antinucleus/pen-plotter/Electrical Design/Media/EasyEDA Design/Bottom.png

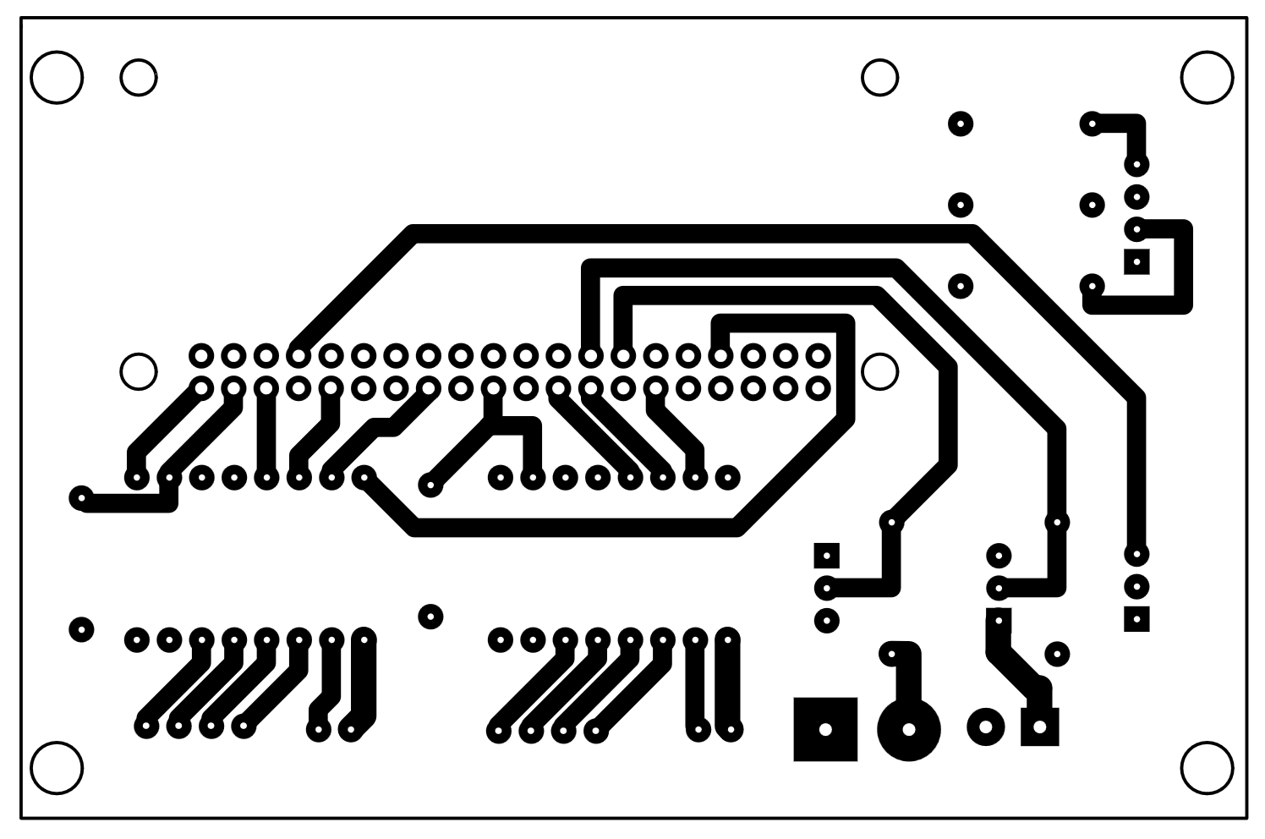
Electrical Design/Media/EasyEDA Design/Bottom.png
