antinucleus/pen-plotter/Electrical Design/Media/EasyEDA Design/Top.png

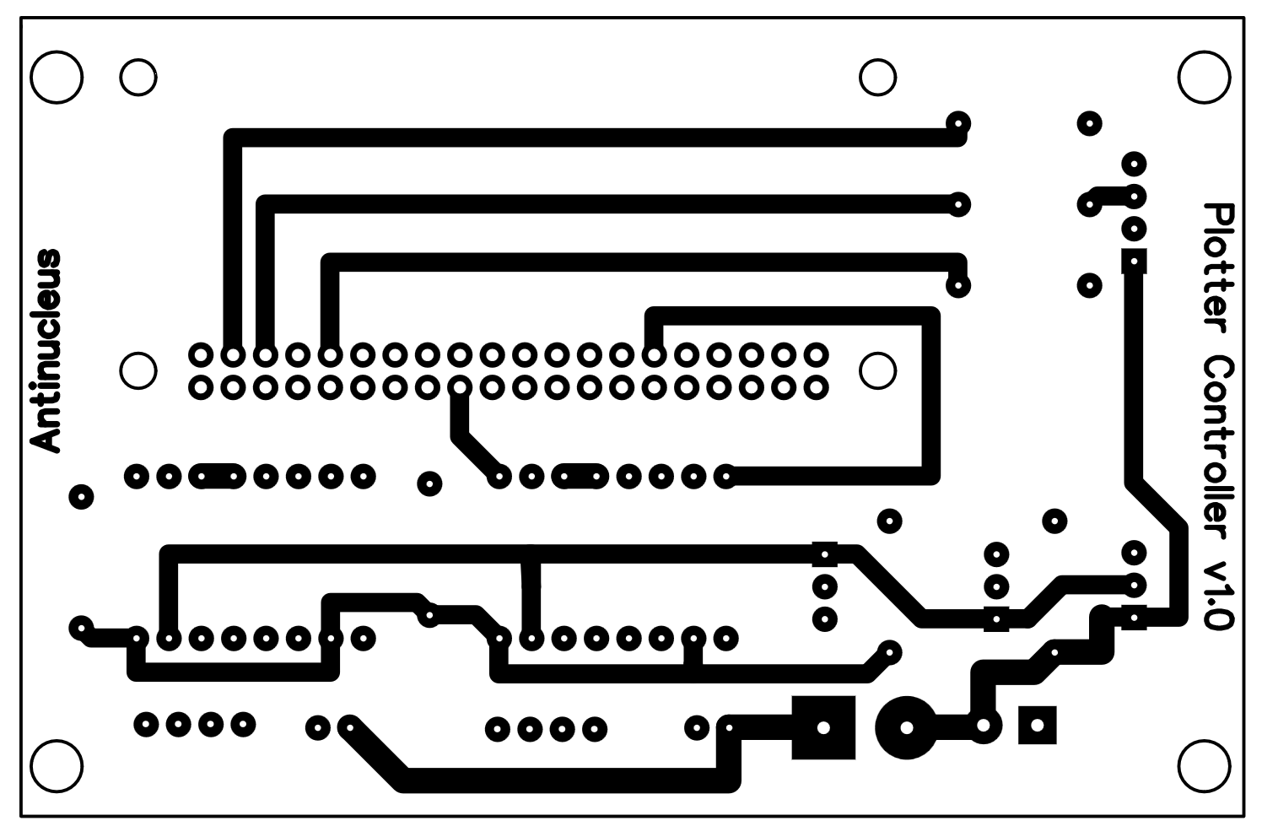
Electrical Design/Media/EasyEDA Design/Top.png
