antinucleus/pen-plotter/Electrical Design/Media/Realized Photos/b.png

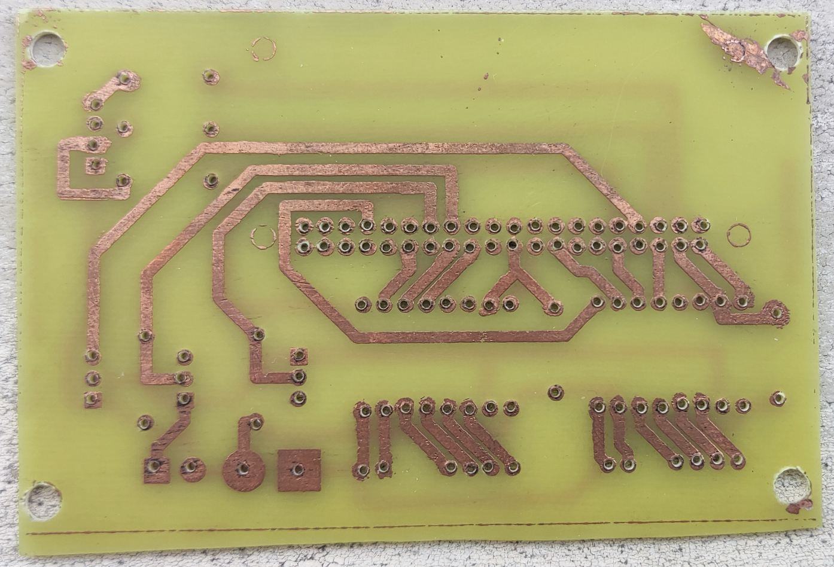
Electrical Design/Media/Realized Photos/b.png
