antinucleus/pen-plotter/Electrical Design/Media/Realized Photos/t.png

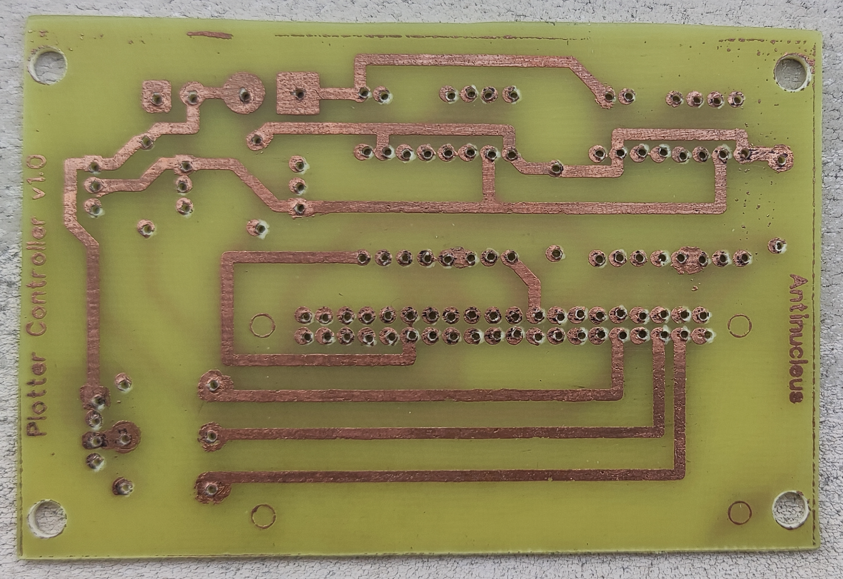
Electrical Design/Media/Realized Photos/t.png
