antinucleus/pen-plotter/Mechanical Design/Media/Fusion360 Design Images/izo.png

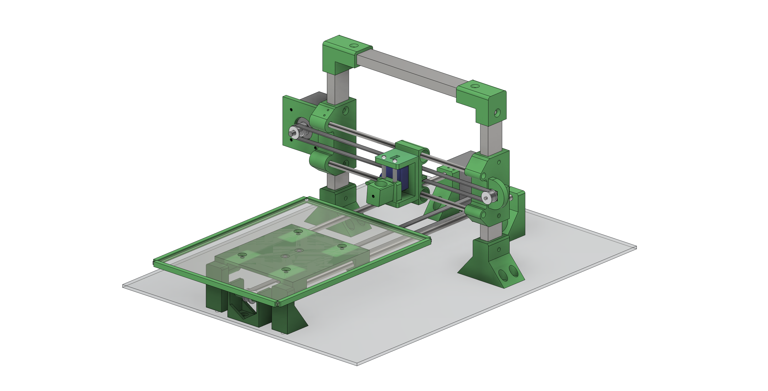
Mechanical Design/Media/Fusion360 Design Images/izo.png
