antinucleus/pen-plotter/Mechanical Design/Media/Fusion360 Design Images/right.png

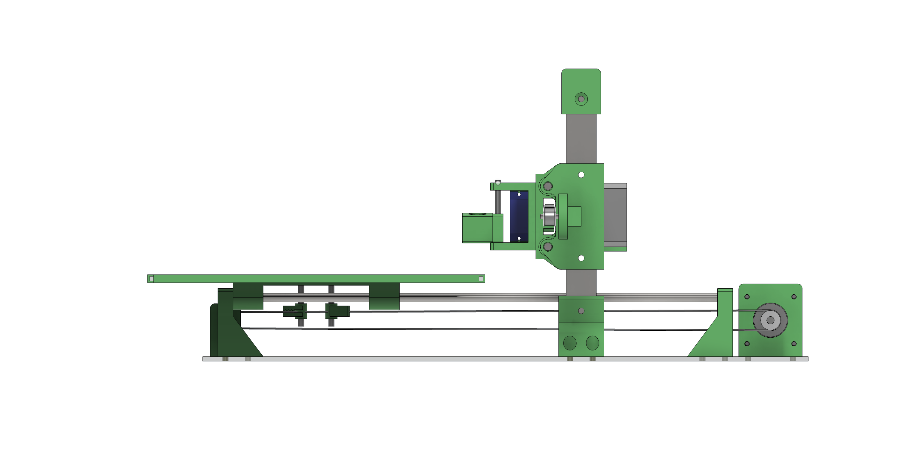
Mechanical Design/Media/Fusion360 Design Images/right.png
