antinucleus/pen-plotter/Mechanical Design/Media/Realized Machine Photos/back.jpg

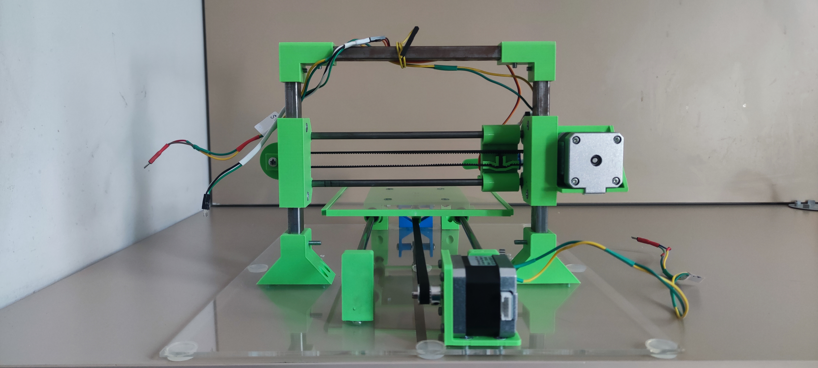
Mechanical Design/Media/Realized Machine Photos/back.jpg
