antinucleus/pen-plotter/Mechanical Design/Media/Realized Machine Photos/front.jpg

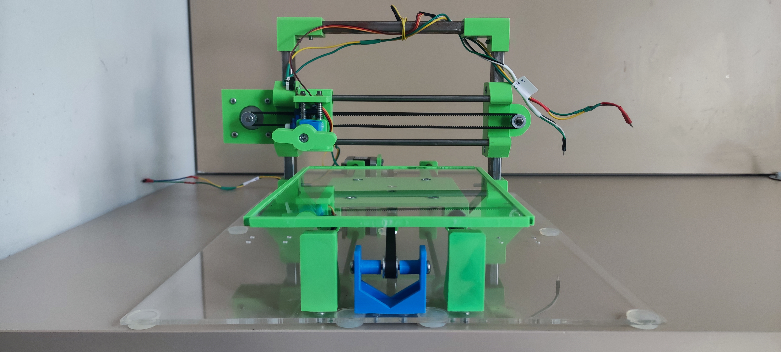
Mechanical Design/Media/Realized Machine Photos/front.jpg
