antinucleus/pen-plotter/Mechanical Design/Media/Realized Machine Photos/izo.jpg

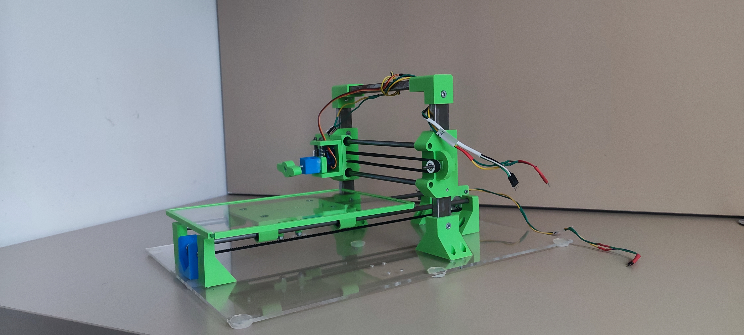
Mechanical Design/Media/Realized Machine Photos/izo.jpg
