antinucleus/pen-plotter/Mechanical Design/Media/Realized Machine Photos/left.jpg

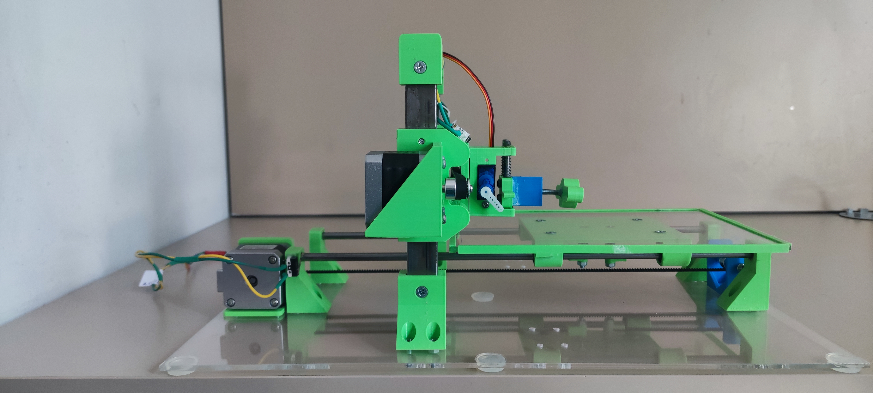
Mechanical Design/Media/Realized Machine Photos/left.jpg
