antinucleus/pen-plotter/Mechanical Design/Media/Realized Machine Photos/right.jpg

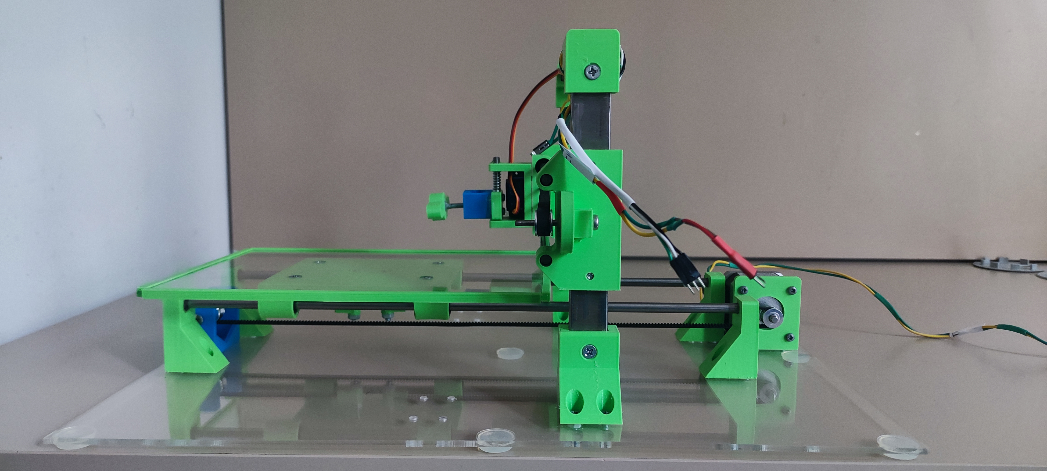
Mechanical Design/Media/Realized Machine Photos/right.jpg
